jonschultz/colorclassic_video_processor/images/bare_board2.PNG

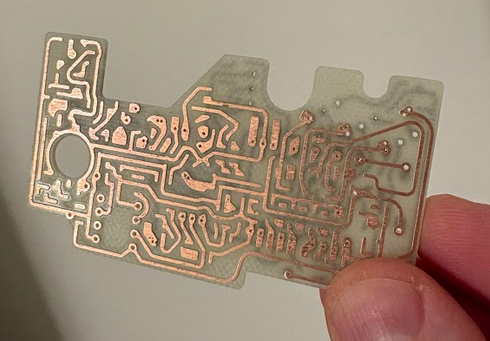
images/bare_board2.PNG
