jonschultz/colorclassic_video_processor/images/boot1.PNG

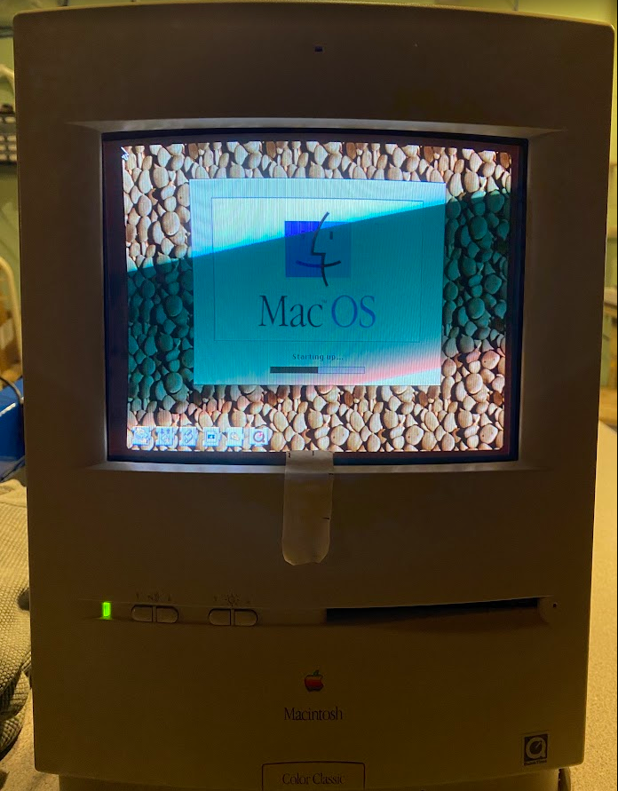
images/boot1.PNG
