jonschultz/colorclassic_video_processor/images/dewarp1.PNG

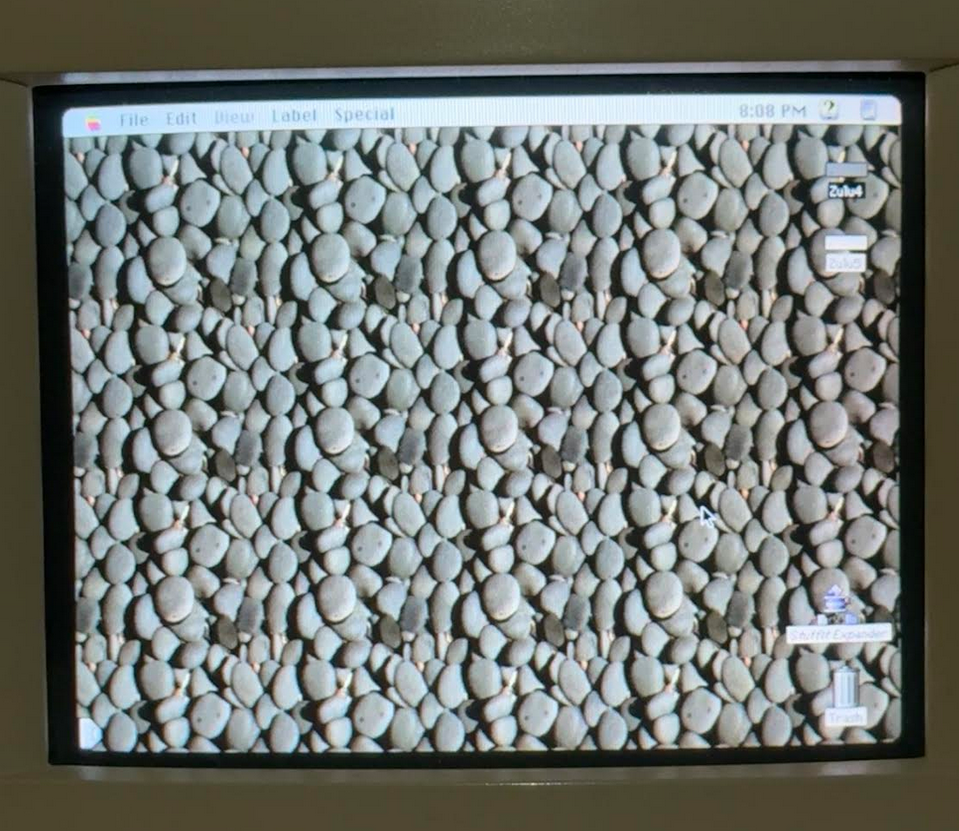
images/dewarp1.PNG
