jonschultz/colorclassic_video_processor/images/PCB_sideA.PNG

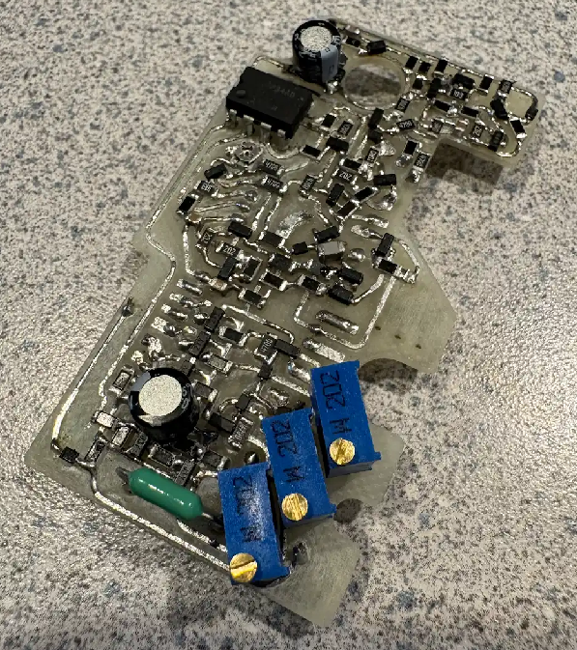
images/PCB_sideA.PNG
