jonschultz/colorclassic_video_processor/images/PCBA3_bottom3.PNG

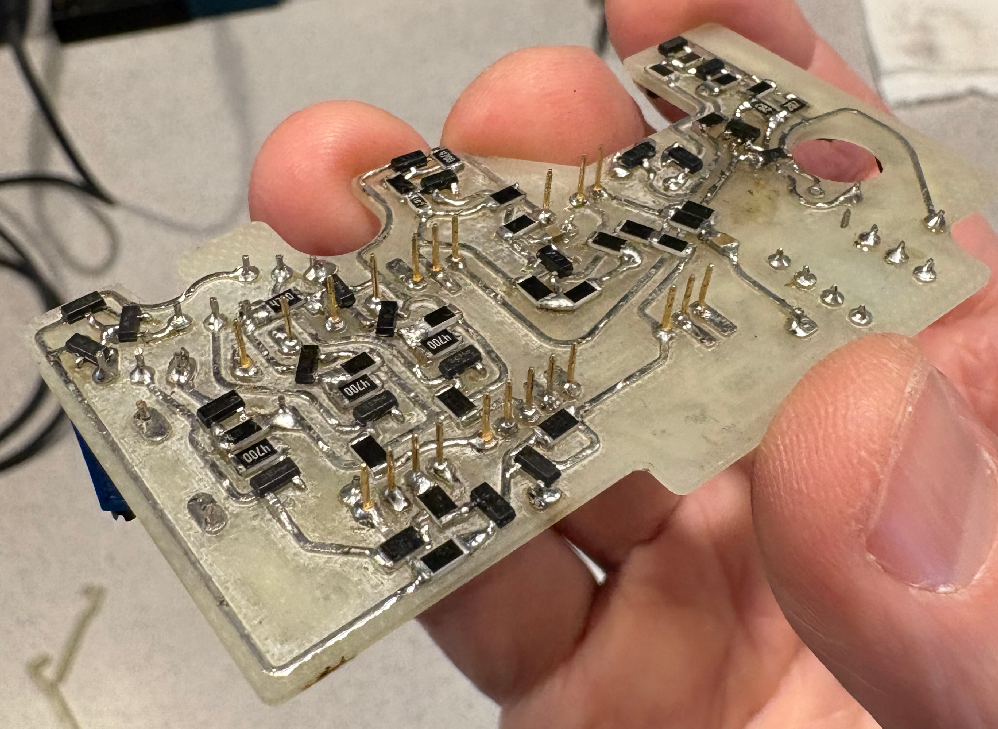
images/PCBA3_bottom3.PNG
