jonschultz/colorclassic_video_processor/images/rgb_pot_adjust1.PNG

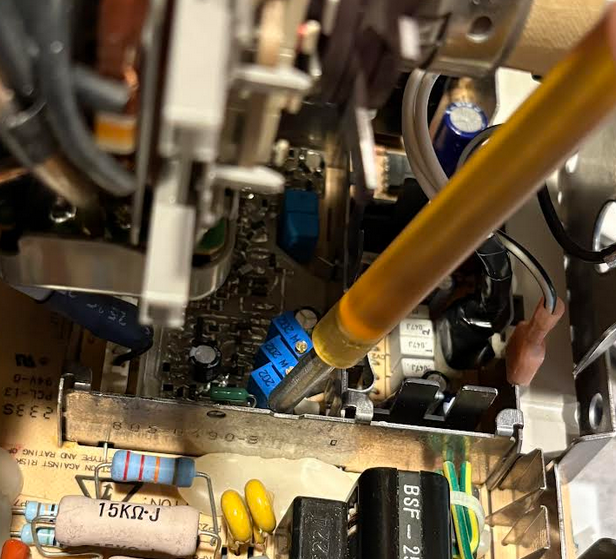
images/rgb_pot_adjust1.PNG
