jonschultz/colorclassic_video_processor/images/video_integrated_PCBA3_pins.PNG

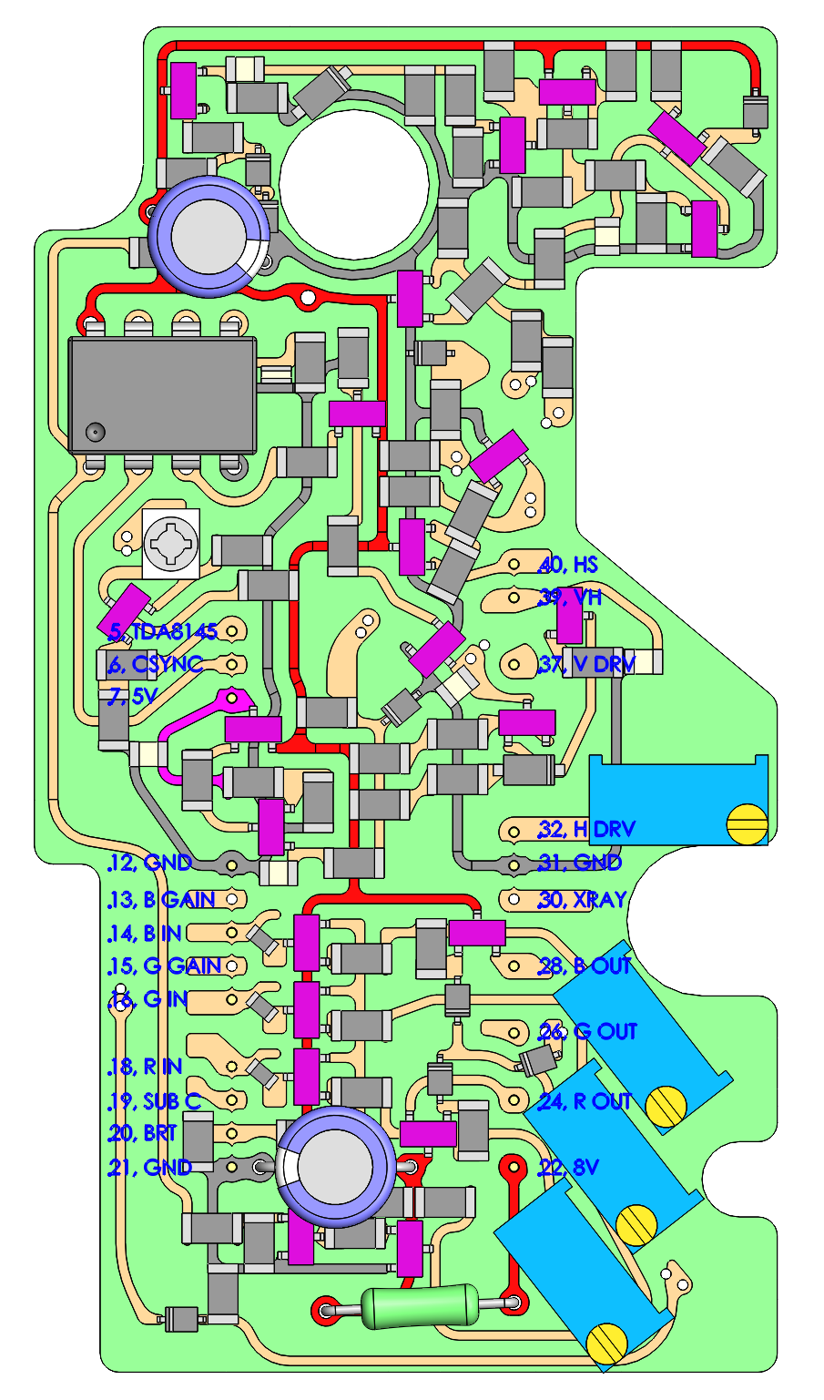
images/video_integrated_PCBA3_pins.PNG
