jonschultz/colorclassic_video_processor/images/video_integrated_PCBA3_top_ortho.PNG

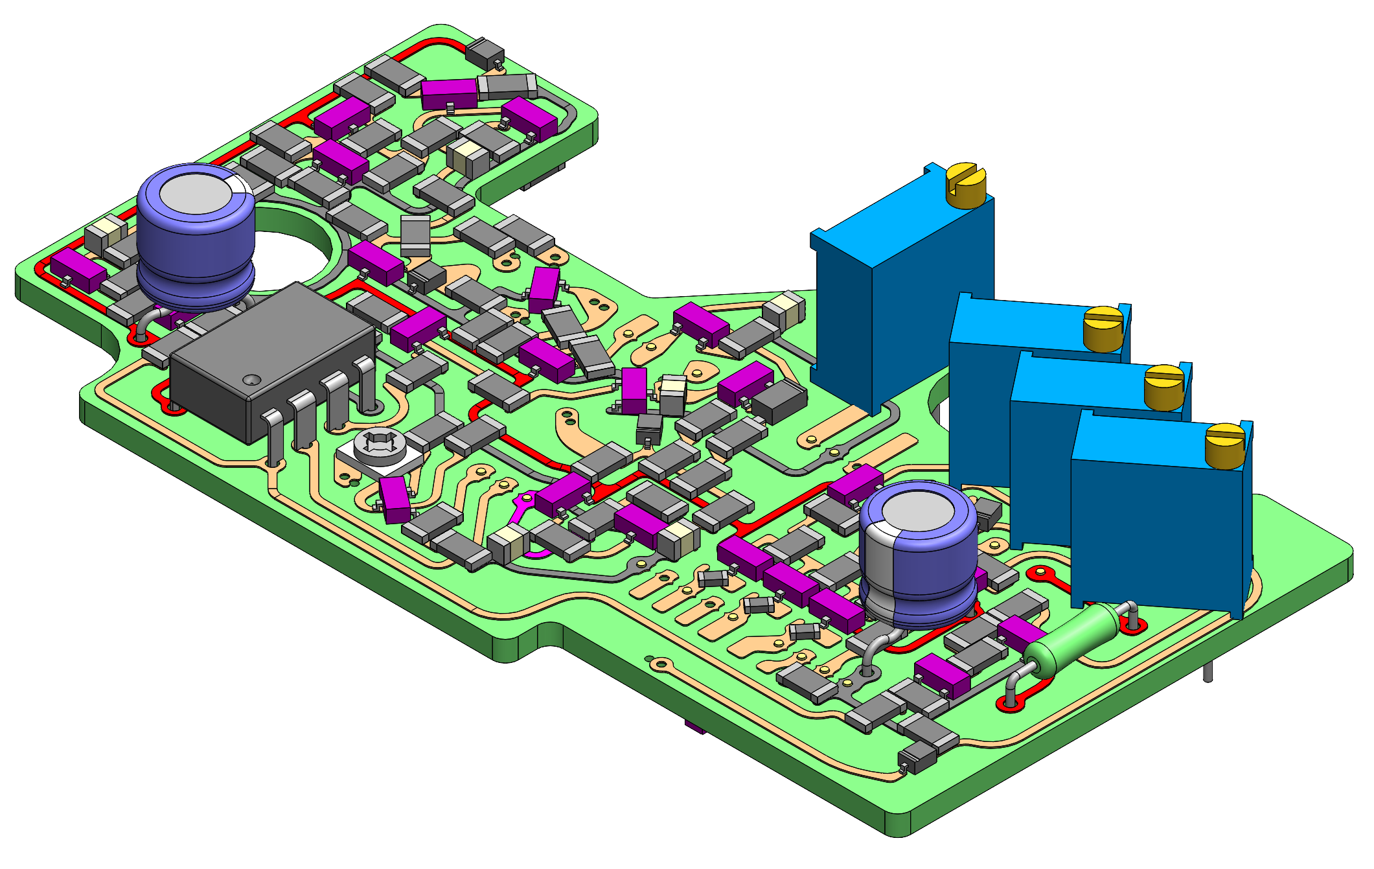
images/video_integrated_PCBA3_top_ortho.PNG
