jonschultz/colorclassic_video_processor/images/video_integrated_PCBA3_vias.PNG

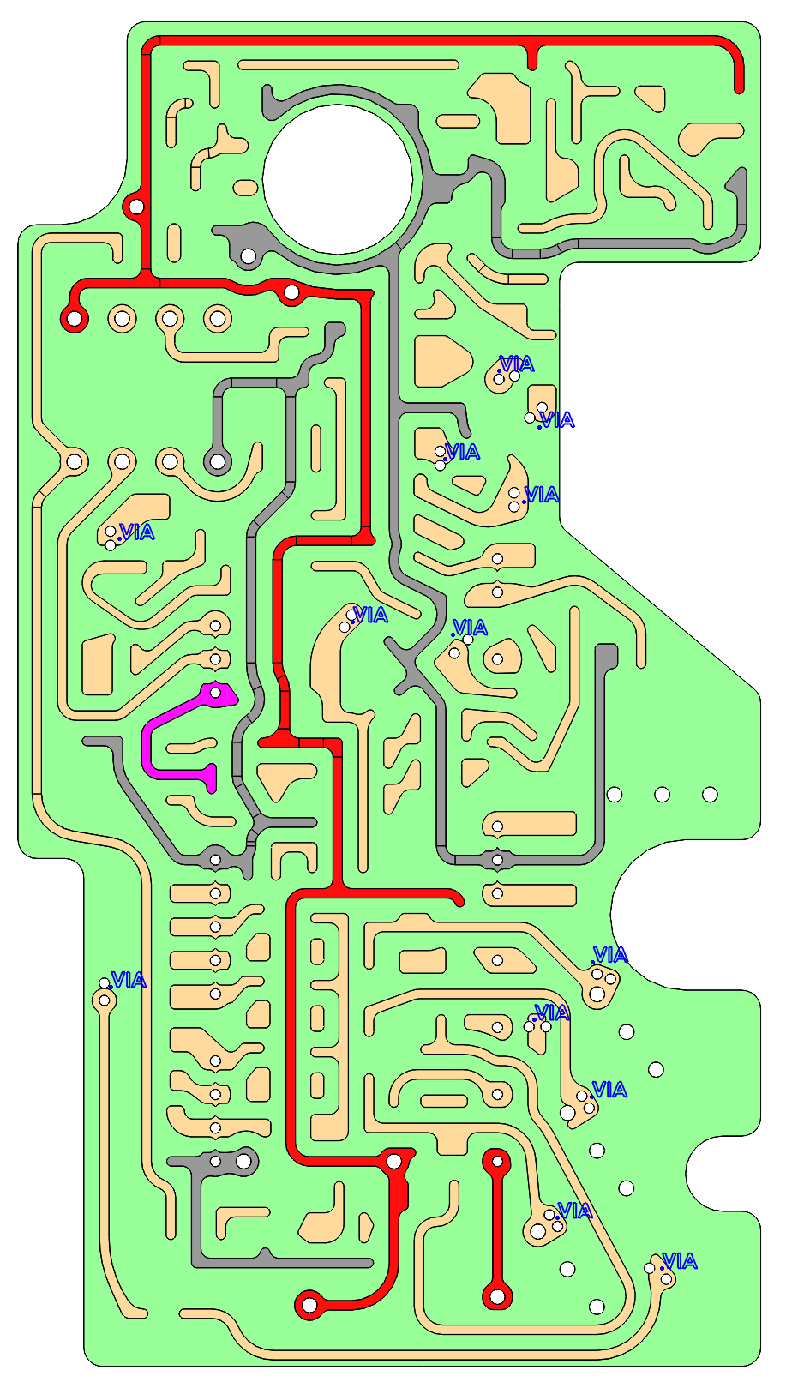
images/video_integrated_PCBA3_vias.PNG
