jonschultz/colorclassic_video_processor/images/video_schem_20251102A.png

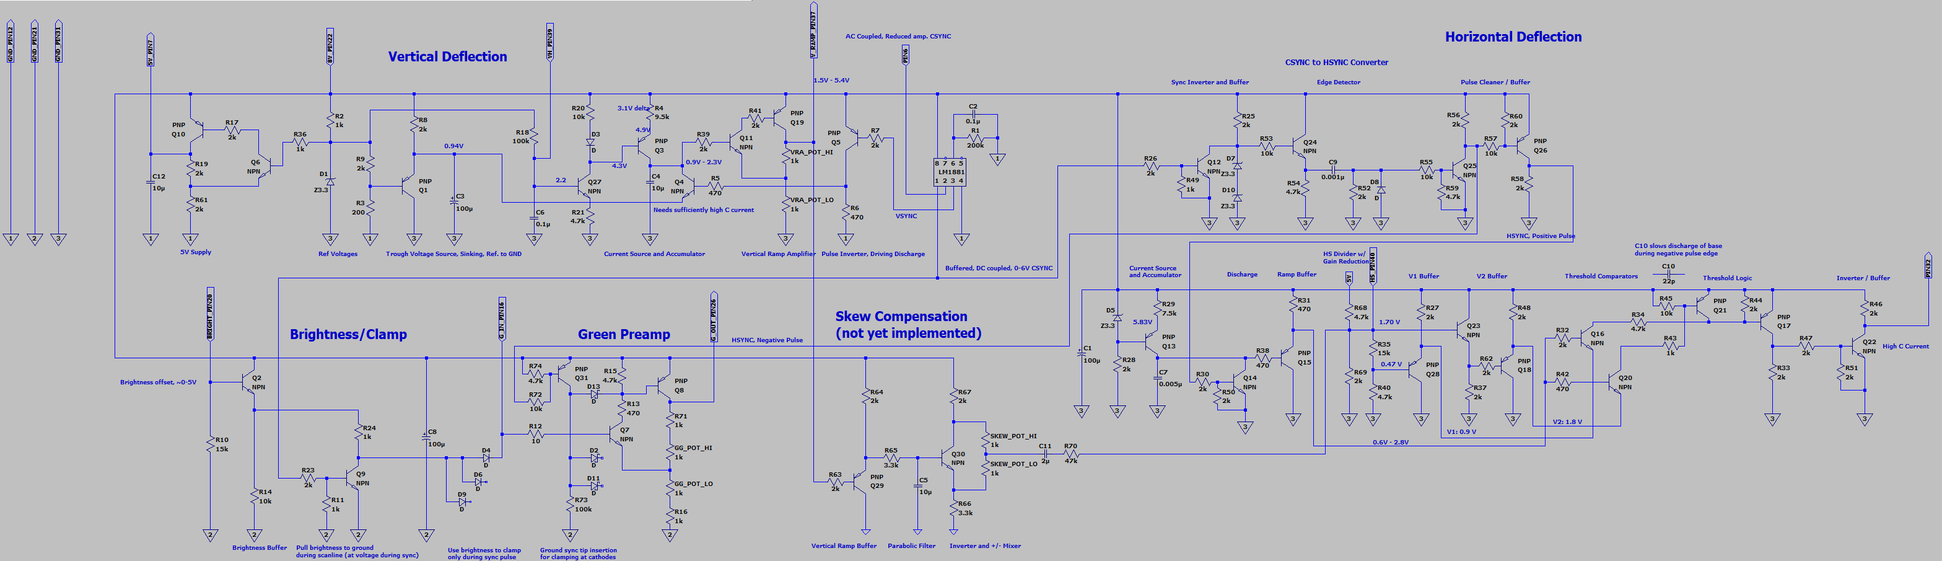
images/video_schem_20251102A.png
