jonschultz/colorclassic_video_processor/images/video_schem_20251117A.png

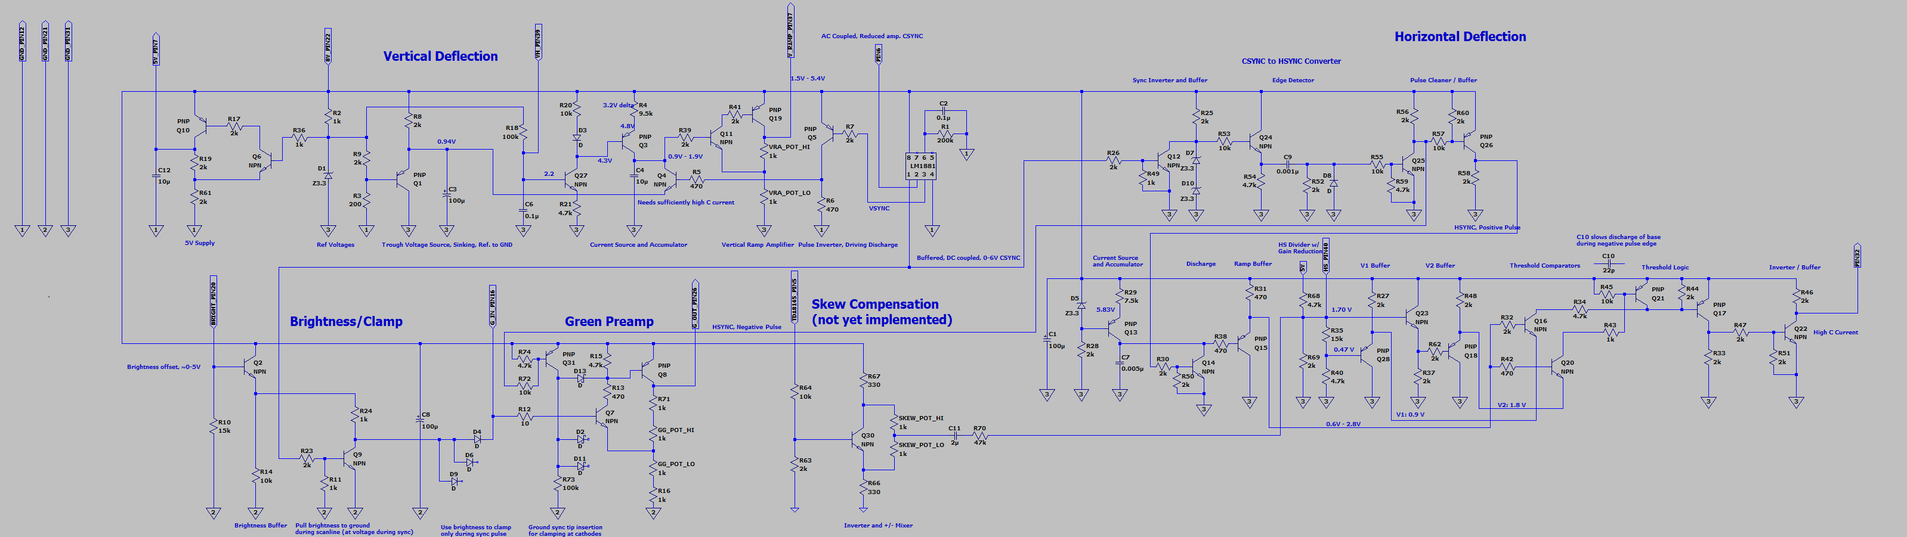
images/video_schem_20251117A.png
