jonschultz/colorclassic_video_processor/images/video_schem_20260513A.png

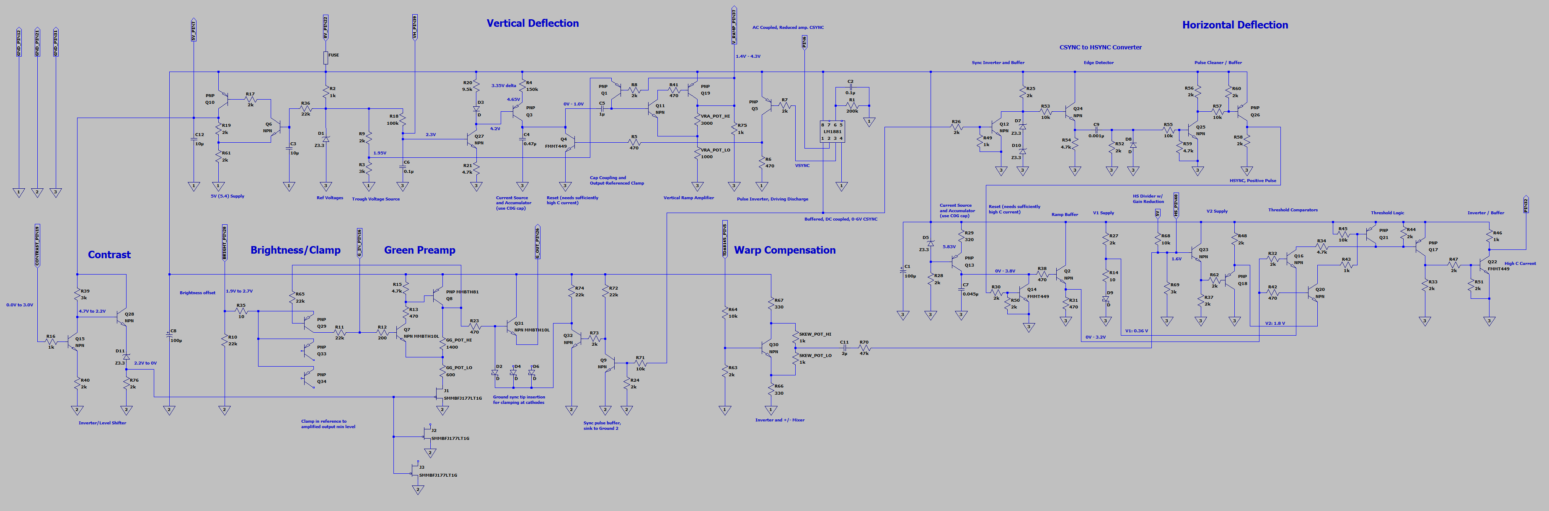
images/video_schem_20260513A.png
