jonschultz/colorclassic_video_processor/images/warp1.PNG

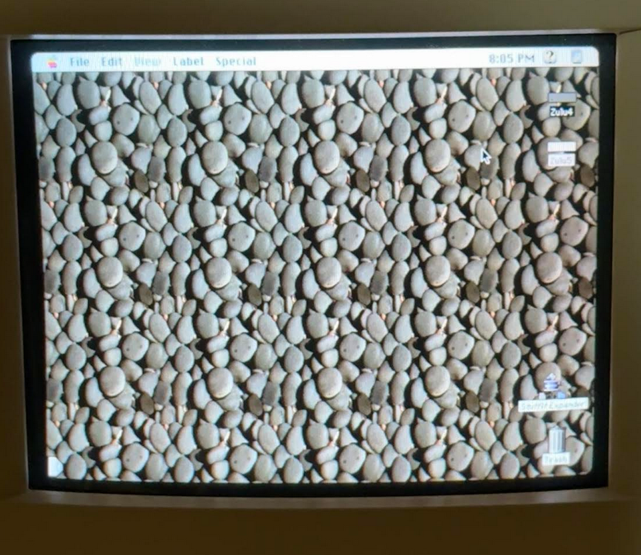
images/warp1.PNG
