jonschultz/colorclassic_video_processor/images/warp_adjust2.PNG

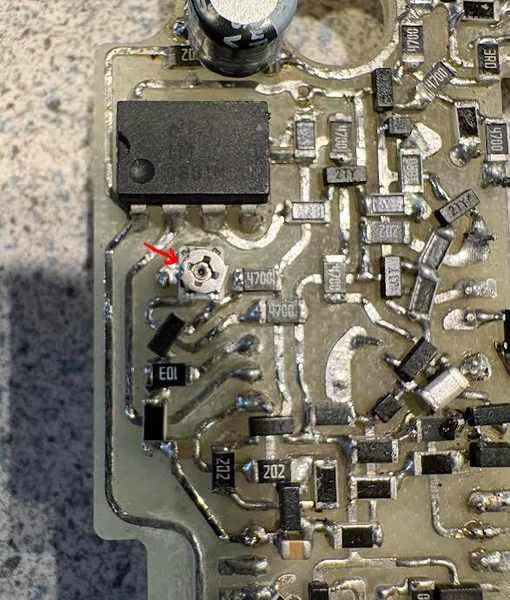
images/warp_adjust2.PNG
