jonschultz/colorclassic_video_processor/images/warp_bodge1.PNG

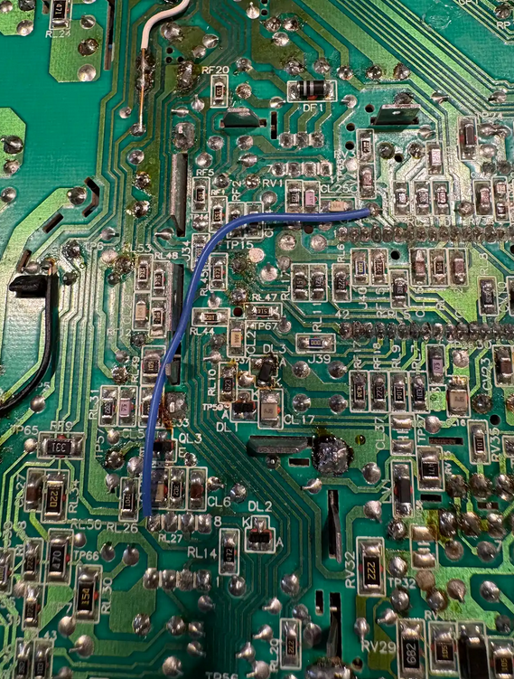
images/warp_bodge1.PNG
