jonschultz/colorclassic_video_processor/images/pcb_installed1.PNG

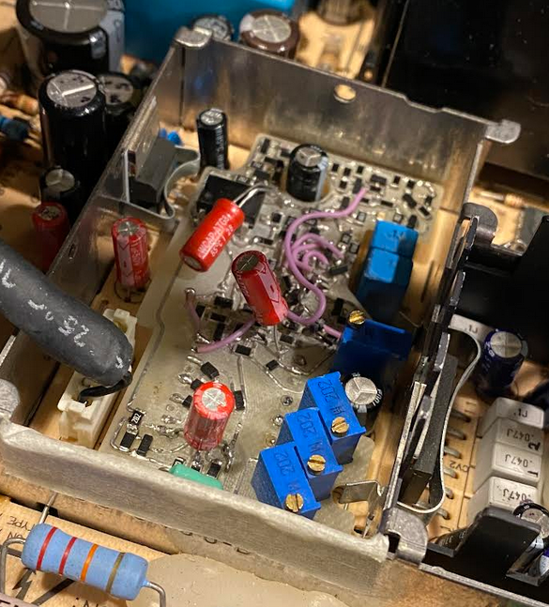
images/pcb_installed1.PNG
