jonschultz/colorclassic_video_processor/images/PCB_installed2.PNG

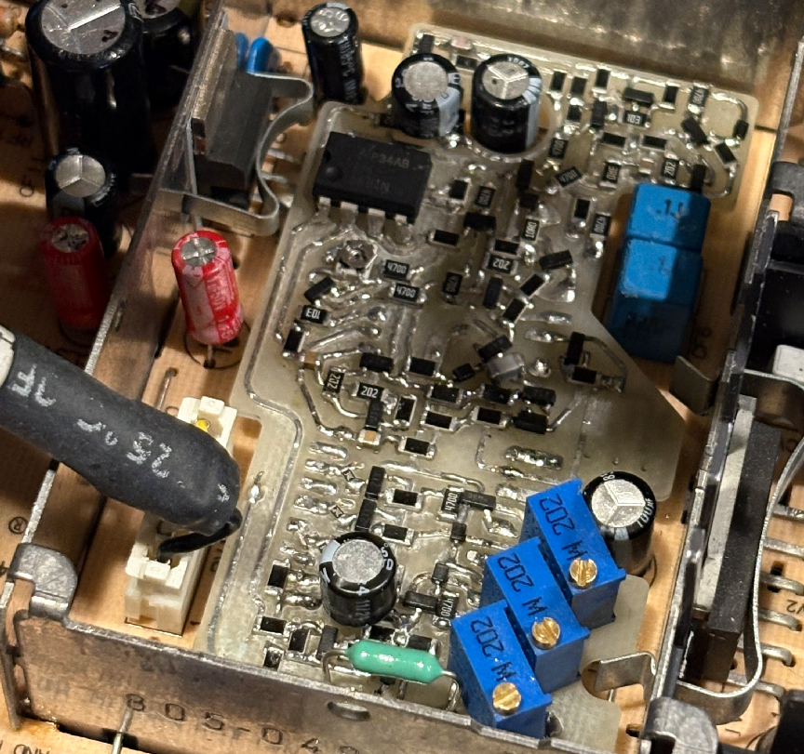
images/PCB_installed2.PNG
