jonschultz/colorclassic_video_processor/images/PCB_installed.PNG

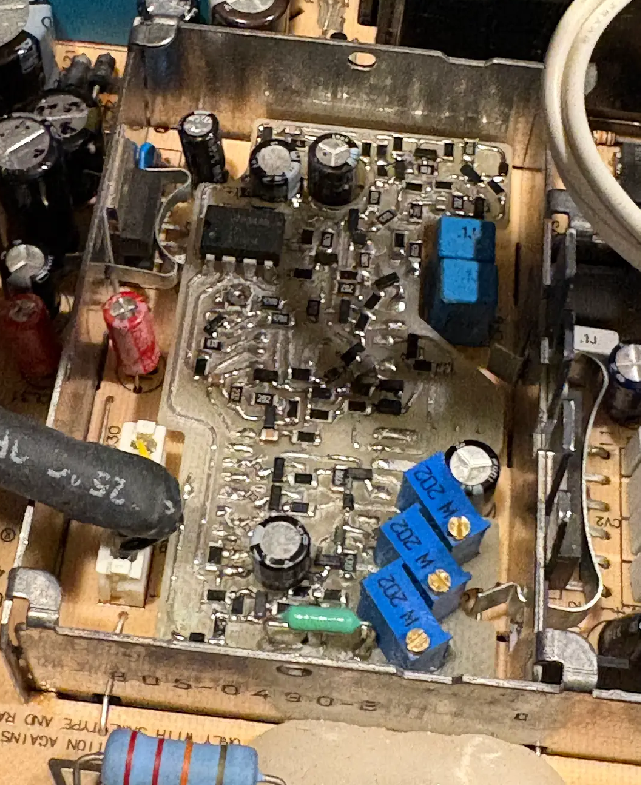
images/PCB_installed.PNG
